gvi70000/STM32-DIY-Reflow-Soldering-Station/Core/Inc/gpio.h

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
/* Define to prevent recursive inclusion -------------------------------------*/
#ifndef __GPIO_H__
#define __GPIO_H__

#ifdef __cplusplus
extern "C" {
#endif

/* Includes ------------------------------------------------------------------*/
#include "main.h"

/* USER CODE BEGIN Private defines */
	extern volatile uint8_t BtnPressed;
	#define FAN_ON GPIOA->ODR |= GPIO_PIN_5;
	#define FAN_OFF GPIOA->ODR &= ~GPIO_PIN_5;
	#define HEAT_ON GPIOA->ODR |= GPIO_PIN_6;
	#define HEAT_OFF GPIOA->ODR &= ~GPIO_PIN_6;	
	#define BUZZ_ON GPIOA->ODR |= GPIO_PIN_7;
	#define BUZZ_OFF GPIOA->ODR &= ~GPIO_PIN_7;
	
/* USER CODE END Private defines */

void MX_GPIO_Init(void);

#ifdef __cplusplus
}
#endif
#endif /*__ GPIO_H__ */
