gvi70000/STM32-DIY-Reflow-Soldering-Station/Core/Src/adc.c

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
/* Includes ------------------------------------------------------------------*/
#include "adc.h"

/* USER CODE BEGIN 0 */
#include <math.h>
#include <stdio.h>
#define ONE					1.0f
#define TEMP_OFFSET	0.0f
#define K						273.15f //0°C in Kelvin
#define Beta				3950.0f //B-coefficient of the thermistor
#define ADC_RES			4096.0f //12 bit ADC value for 3.3V
#define T0					(K + 25.0f) //25°C in Kelvin
#define INV_T0			(ONE/T0) 
#define ADC_SIZE		64

//100k NTC measured resistance in Ohms @ 25C
const float R1[2] = {99000.0, 101000.0};
//10k resistor measured resistance in Ohms @ 25C
const float R2[2] = {10440, 10450.0};
//Calculated temperature
volatile float crtTemp, t1, t2;

uint16_t ntc1_Val[ADC_SIZE];
uint16_t ntc2_Val[ADC_SIZE];
/* USER CODE END 0 */

ADC_HandleTypeDef hadc1;
ADC_HandleTypeDef hadc2;
DMA_HandleTypeDef hdma_adc1;
DMA_HandleTypeDef hdma_adc2;

/* ADC1 init function */
void MX_ADC1_Init(void)
{

  ADC_MultiModeTypeDef multimode = {0};
  ADC_ChannelConfTypeDef sConfig = {0};

  /** Common config
  */
  hadc1.Instance = ADC1;
  hadc1.Init.ClockPrescaler = ADC_CLOCK_ASYNC_DIV1;
  hadc1.Init.Resolution = ADC_RESOLUTION_12B;
  hadc1.Init.ScanConvMode = ADC_SCAN_DISABLE;
  hadc1.Init.ContinuousConvMode = ENABLE;
  hadc1.Init.DiscontinuousConvMode = DISABLE;
  hadc1.Init.ExternalTrigConvEdge = ADC_EXTERNALTRIGCONVEDGE_NONE;
  hadc1.Init.ExternalTrigConv = ADC_SOFTWARE_START;
  hadc1.Init.DataAlign = ADC_DATAALIGN_RIGHT;
  hadc1.Init.NbrOfConversion = 1;
  hadc1.Init.DMAContinuousRequests = ENABLE;
  hadc1.Init.EOCSelection = ADC_EOC_SINGLE_CONV;
  hadc1.Init.LowPowerAutoWait = DISABLE;
  hadc1.Init.Overrun = ADC_OVR_DATA_OVERWRITTEN;
  if (HAL_ADC_Init(&hadc1) != HAL_OK)
  {
    Error_Handler();
  }

  /** Configure Regular Channel
  */
  sConfig.Channel = ADC_CHANNEL_4;
  sConfig.Rank = ADC_REGULAR_RANK_1;
  sConfig.SingleDiff = ADC_SINGLE_ENDED;
  sConfig.SamplingTime = ADC_SAMPLETIME_601CYCLES_5;
  sConfig.OffsetNumber = ADC_OFFSET_NONE;
  sConfig.Offset = 0;
  if (HAL_ADC_ConfigChannel(&hadc1, &sConfig) != HAL_OK)
  {
    Error_Handler();
  }
}
/* ADC2 init function */
void MX_ADC2_Init(void)
{

  ADC_ChannelConfTypeDef sConfig = {0};

  /** Common config
  */
  hadc2.Instance = ADC2;
  hadc2.Init.ClockPrescaler = ADC_CLOCK_ASYNC_DIV1;
  hadc2.Init.Resolution = ADC_RESOLUTION_12B;
  hadc2.Init.ScanConvMode = ADC_SCAN_DISABLE;
  hadc2.Init.ContinuousConvMode = ENABLE;
  hadc2.Init.DiscontinuousConvMode = DISABLE;
  hadc2.Init.ExternalTrigConvEdge = ADC_EXTERNALTRIGCONVEDGE_NONE;
  hadc2.Init.ExternalTrigConv = ADC_SOFTWARE_START;
  hadc2.Init.DataAlign = ADC_DATAALIGN_RIGHT;
  hadc2.Init.NbrOfConversion = 1;
  hadc2.Init.DMAContinuousRequests = ENABLE;
  hadc2.Init.EOCSelection = ADC_EOC_SINGLE_CONV;
  hadc2.Init.LowPowerAutoWait = DISABLE;
  hadc2.Init.Overrun = ADC_OVR_DATA_OVERWRITTEN;
  if (HAL_ADC_Init(&hadc2) != HAL_OK)
  {
    Error_Handler();
  }

  /** Configure Regular Channel
  */
  sConfig.Channel = ADC_CHANNEL_1;
  sConfig.Rank = ADC_REGULAR_RANK_1;
  sConfig.SingleDiff = ADC_SINGLE_ENDED;
  sConfig.SamplingTime = ADC_SAMPLETIME_601CYCLES_5;
  sConfig.OffsetNumber = ADC_OFFSET_NONE;
  sConfig.Offset = 0;
  if (HAL_ADC_ConfigChannel(&hadc2, &sConfig) != HAL_OK)
  {
    Error_Handler();
  }
}

static uint32_t HAL_RCC_ADC12_CLK_ENABLED=0;

void HAL_ADC_MspInit(ADC_HandleTypeDef* adcHandle)
{

  GPIO_InitTypeDef GPIO_InitStruct = {0};
  if(adcHandle->Instance==ADC1)
  {
    /* ADC1 clock enable */
    HAL_RCC_ADC12_CLK_ENABLED++;
    if(HAL_RCC_ADC12_CLK_ENABLED==1){
      __HAL_RCC_ADC12_CLK_ENABLE();
    }

    __HAL_RCC_GPIOA_CLK_ENABLE();
    /**ADC1 GPIO Configuration
    PA3     ------> ADC1_IN4
    */
    GPIO_InitStruct.Pin = NTC1_Pin;
    GPIO_InitStruct.Mode = GPIO_MODE_ANALOG;
    GPIO_InitStruct.Pull = GPIO_NOPULL;
    HAL_GPIO_Init(NTC1_GPIO_Port, &GPIO_InitStruct);

    /* ADC1 DMA Init */
    /* ADC1 Init */
    hdma_adc1.Instance = DMA1_Channel1;
    hdma_adc1.Init.Direction = DMA_PERIPH_TO_MEMORY;
    hdma_adc1.Init.PeriphInc = DMA_PINC_DISABLE;
    hdma_adc1.Init.MemInc = DMA_MINC_ENABLE;
    hdma_adc1.Init.PeriphDataAlignment = DMA_PDATAALIGN_HALFWORD;
    hdma_adc1.Init.MemDataAlignment = DMA_MDATAALIGN_HALFWORD;
    hdma_adc1.Init.Mode = DMA_CIRCULAR;
    hdma_adc1.Init.Priority = DMA_PRIORITY_LOW;
    if (HAL_DMA_Init(&hdma_adc1) != HAL_OK)
    {
      Error_Handler();
    }

    __HAL_LINKDMA(adcHandle,DMA_Handle,hdma_adc1);

  }
  else if(adcHandle->Instance==ADC2)
  {
    /* ADC2 clock enable */
    HAL_RCC_ADC12_CLK_ENABLED++;
    if(HAL_RCC_ADC12_CLK_ENABLED==1){
      __HAL_RCC_ADC12_CLK_ENABLE();
    }

    __HAL_RCC_GPIOA_CLK_ENABLE();
    /**ADC2 GPIO Configuration
    PA4     ------> ADC2_IN1
    */
    GPIO_InitStruct.Pin = NTC2_Pin;
    GPIO_InitStruct.Mode = GPIO_MODE_ANALOG;
    GPIO_InitStruct.Pull = GPIO_NOPULL;
    HAL_GPIO_Init(NTC2_GPIO_Port, &GPIO_InitStruct);

    /* ADC2 DMA Init */
    /* ADC2 Init */
    hdma_adc2.Instance = DMA2_Channel1;
    hdma_adc2.Init.Direction = DMA_PERIPH_TO_MEMORY;
    hdma_adc2.Init.PeriphInc = DMA_PINC_DISABLE;
    hdma_adc2.Init.MemInc = DMA_MINC_ENABLE;
    hdma_adc2.Init.PeriphDataAlignment = DMA_PDATAALIGN_HALFWORD;
    hdma_adc2.Init.MemDataAlignment = DMA_MDATAALIGN_HALFWORD;
    hdma_adc2.Init.Mode = DMA_CIRCULAR;
    hdma_adc2.Init.Priority = DMA_PRIORITY_LOW;
    if (HAL_DMA_Init(&hdma_adc2) != HAL_OK)
    {
      Error_Handler();
    }

    __HAL_LINKDMA(adcHandle,DMA_Handle,hdma_adc2);

  }
}

void HAL_ADC_MspDeInit(ADC_HandleTypeDef* adcHandle)
{

  if(adcHandle->Instance==ADC1)
  {
    /* Peripheral clock disable */
    HAL_RCC_ADC12_CLK_ENABLED--;
    if(HAL_RCC_ADC12_CLK_ENABLED==0){
      __HAL_RCC_ADC12_CLK_DISABLE();
    }

    /**ADC1 GPIO Configuration
    PA3     ------> ADC1_IN4
    */
    HAL_GPIO_DeInit(NTC1_GPIO_Port, NTC1_Pin);

    /* ADC1 DMA DeInit */
    HAL_DMA_DeInit(adcHandle->DMA_Handle);
  }
  else if(adcHandle->Instance==ADC2)
  {
    /* Peripheral clock disable */
    HAL_RCC_ADC12_CLK_ENABLED--;
    if(HAL_RCC_ADC12_CLK_ENABLED==0){
      __HAL_RCC_ADC12_CLK_DISABLE();
    }

    /**ADC2 GPIO Configuration
    PA4     ------> ADC2_IN1
    */
    HAL_GPIO_DeInit(NTC2_GPIO_Port, NTC2_Pin);

    /* ADC2 DMA DeInit */
    HAL_DMA_DeInit(adcHandle->DMA_Handle);
  }
}

/* USER CODE BEGIN 1 */
void startADC(){
	//Start ADC
	HAL_ADC_Start_DMA(&hadc1, (uint32_t*)ntc1_Val, ADC_SIZE);
	HAL_ADC_Start_DMA(&hadc2, (uint32_t*)ntc2_Val, ADC_SIZE);
}

void stopADC(){
	//Start ADC
	HAL_ADC_Stop(&hadc1);
	HAL_ADC_Stop(&hadc2);
}

static float calculateNTCTemperature(uint8_t idx, uint16_t* adcValues) {
  uint32_t sum = 0;
  for (uint8_t i = 0; i < ADC_SIZE; i++) {
    sum += adcValues[i];
  }
  float avgAdcValue = (float)sum / ADC_SIZE;
  float r_ntc = R2[idx] * (ADC_RES / avgAdcValue - 1.0);
  return (1.0 / (INV_T0 + 1.0 / Beta * log(r_ntc / R1[idx])) - K);
}

//Resistors as per link below, R1(Rntc) is the NTC and R2 is 100kOhm
//https://ohmslawcalculator.com/voltage-divider-calculator
void HAL_ADC_ConvCpltCallback(ADC_HandleTypeDef* hadc) {
  if (hadc->Instance == ADC1) {
    t1 = calculateNTCTemperature(0, ntc1_Val);
  }
  if (hadc->Instance == ADC2) {
    t2 = calculateNTCTemperature(1, ntc2_Val);
  }
	float medT = (t1 + t2) / 2.0;
	float medT2 = medT*medT;
  crtTemp = -0.0006*medT2 + 1.2193*medT +2.3892;
}
/* USER CODE END 1 */
