gvi70000/STM32-DIY-Reflow-Soldering-Station/ST7735/GFX_FUNCTIONS.c

#include <ST7735.h>
#include "stdint.h"
#include "stdlib.h"


extern uint8_t _width;       ///< Display width as modified by current rotation
extern uint8_t _height;      ///< Display height as modified by current rotation
extern uint8_t cursor_x;     ///< x location to start print()ing text
extern uint8_t cursor_y;     ///< y location to start print()ing text
extern uint8_t rotation;     ///< Display rotation (0 thru 3)
extern uint8_t _colstart;   ///< Some displays need this changed to offset
extern uint8_t _rowstart;       ///< Some displays need this changed to offset
extern uint8_t _xstart;
extern uint8_t _ystart;


void drawPixel(uint8_t x, uint8_t y, uint16_t color) {
	ST7735_DrawPixel(x, y, color);
}

void fillRect(uint8_t x, uint8_t y, uint8_t w, uint8_t h, uint16_t color) {
	ST7735_FillRectangle(x, y, w, h, color);
}


/***********************************************************************************************************/


#define _swap_int8_t(a, b)                                                    \
  {                                                                            \
    uint8_t t = a;                                                             \
    a = b;                                                                     \
    b = t;                                                                     \
  }

#define min(a, b) (((a) < (b)) ? (a) : (b))


void writePixel(uint8_t x, uint8_t y, uint16_t color) {
    drawPixel(x, y, color);
}

void writeLine(uint8_t x0, uint8_t y0, uint8_t x1, uint8_t y1, uint16_t color) {
    int8_t steep = abs(y1 - y0) > abs(x1 - x0);
    if (steep) {
        _swap_int8_t(x0, y0);
        _swap_int8_t(x1, y1);
    }

    if (x0 > x1) {
        _swap_int8_t(x0, x1);
        _swap_int8_t(y0, y1);
    }

    int8_t dx, dy;
    dx = x1 - x0;
    dy = abs(y1 - y0);

    int8_t err = dx / 2;
    int8_t ystep;

    if (y0 < y1) {
        ystep = 1;
    } else {
        ystep = -1;
    }

    for (; x0<=x1; x0++) {
        if (steep) {
            writePixel(y0, x0, color);
        } else {
            writePixel(x0, y0, color);
        }
        err -= dy;
        if (err < 0) {
            y0 += ystep;
            err += dx;
        }
    }
}

void  drawFastVLine(uint8_t x, uint8_t y, uint8_t h, uint16_t color) {
	writeLine(x, y, x, y + h - 1, color);
}
void  drawFastHLine(uint8_t x, uint8_t y, uint8_t w, uint16_t color) {
	writeLine(x, y, x + w - 1, y, color);
}

void drawLine(uint8_t x0, uint8_t y0, uint8_t x1, uint8_t y1, uint16_t color) {
    if(x0 == x1){
        if(y0 > y1) _swap_int8_t(y0, y1);
        drawFastVLine(x0, y0, y1 - y0 + 1, color);
    } else if(y0 == y1){
        if(x0 > x1) _swap_int8_t(x0, x1);
        drawFastHLine(x0, y0, x1 - x0 + 1, color);
    } else {
        writeLine(x0, y0, x1, y1, color);
    }
}

void drawCircle(uint8_t x0, uint8_t y0, uint8_t r, uint16_t color) {
    uint8_t f = 1 - r;
    uint8_t ddF_x = 1;
    uint8_t ddF_y = -2 * r;
    uint8_t x = 0;
    uint8_t y = r;

    writePixel(x0  , y0+r, color);
    writePixel(x0  , y0-r, color);
    writePixel(x0+r, y0  , color);
    writePixel(x0-r, y0  , color);

    while (x<y) {
        if (f >= 0) {
            y--;
            ddF_y += 2;
            f += ddF_y;
        }
        x++;
        ddF_x += 2;
        f += ddF_x;

        writePixel(x0 + x, y0 + y, color);
        writePixel(x0 - x, y0 + y, color);
        writePixel(x0 + x, y0 - y, color);
        writePixel(x0 - x, y0 - y, color);
        writePixel(x0 + y, y0 + x, color);
        writePixel(x0 - y, y0 + x, color);
        writePixel(x0 + y, y0 - x, color);
        writePixel(x0 - y, y0 - x, color);
    }
}

void drawCircleHelper(uint8_t x0, uint8_t y0, uint8_t r, uint8_t cornername, uint16_t color) {
    uint8_t f     = 1 - r;
    uint8_t ddF_x = 1;
    uint8_t ddF_y = -2 * r;
    uint8_t x     = 0;
    uint8_t y     = r;

    while (x<y) {
        if (f >= 0) {
            y--;
            ddF_y += 2;
            f     += ddF_y;
        }
        x++;
        ddF_x += 2;
        f     += ddF_x;
        if (cornername & 0x4) {
            writePixel(x0 + x, y0 + y, color);
            writePixel(x0 + y, y0 + x, color);
        }
        if (cornername & 0x2) {
            writePixel(x0 + x, y0 - y, color);
            writePixel(x0 + y, y0 - x, color);
        }
        if (cornername & 0x8) {
            writePixel(x0 - y, y0 + x, color);
            writePixel(x0 - x, y0 + y, color);
        }
        if (cornername & 0x1) {
            writePixel(x0 - y, y0 - x, color);
            writePixel(x0 - x, y0 - y, color);
        }
    }
}

void fillCircleHelper(uint8_t x0, uint8_t y0, uint8_t r, uint8_t corners, uint8_t delta, uint16_t color) {

    uint8_t f     = 1 - r;
    uint8_t ddF_x = 1;
    uint8_t ddF_y = -2 * r;
    uint8_t x     = 0;
    uint8_t y     = r;
    uint8_t px    = x;
    uint8_t py    = y;

    delta++; // Avoid some +1's in the loop

    while(x < y) {
        if (f >= 0) {
            y--;
            ddF_y += 2;
            f     += ddF_y;
        }
        x++;
        ddF_x += 2;
        f     += ddF_x;
        // These checks avoid double-drawing certain lines, important
        // for the SSD1306 library which has an INVERT drawing mode.
        if(x < (y + 1)) {
            if(corners & 1) drawFastVLine(x0+x, y0-y, 2*y+delta, color);
            if(corners & 2) drawFastVLine(x0-x, y0-y, 2*y+delta, color);
        }
        if(y != py) {
            if(corners & 1) drawFastVLine(x0+py, y0-px, 2*px+delta, color);
            if(corners & 2) drawFastVLine(x0-py, y0-px, 2*px+delta, color);
            py = y;
        }
        px = x;
    }
}

void fillCircle(uint8_t x0, uint8_t y0, uint8_t r, uint16_t color) {
    drawFastVLine(x0, y0-r, 2*r+1, color);
    fillCircleHelper(x0, y0, r, 3, 0, color);
}



void drawRect(uint8_t x, uint8_t y, uint8_t w, uint8_t h, uint16_t color) {
    drawFastHLine(x, y, w, color);
    drawFastHLine(x, y+h-1, w, color);
    drawFastVLine(x, y, h, color);
    drawFastVLine(x+w-1, y, h, color);
}

void drawRoundRect(uint8_t x, uint8_t y, uint8_t w, uint8_t h, uint8_t r, uint16_t color) {
    uint8_t max_radius = ((w < h) ? w : h) / 2; // 1/2 minor axis
    if(r > max_radius) r = max_radius;
    // smarter version
    drawFastHLine(x+r  , y    , w-2*r, color); // Top
    drawFastHLine(x+r  , y+h-1, w-2*r, color); // Bottom
    drawFastVLine(x    , y+r  , h-2*r, color); // Left
    drawFastVLine(x+w-1, y+r  , h-2*r, color); // Right
    // draw four corners
    drawCircleHelper(x+r    , y+r    , r, 1, color);
    drawCircleHelper(x+w-r-1, y+r    , r, 2, color);
    drawCircleHelper(x+w-r-1, y+h-r-1, r, 4, color);
    drawCircleHelper(x+r    , y+h-r-1, r, 8, color);
}


void fillRoundRect(uint8_t x, uint8_t y, uint8_t w, uint8_t h, uint8_t r, uint16_t color) {
    uint8_t max_radius = ((w < h) ? w : h) / 2; // 1/2 minor axis
    if(r > max_radius) r = max_radius;
    // smarter version
    fillRect(x+r, y, w-2*r, h, color);
    // draw four corners
    fillCircleHelper(x+w-r-1, y+r, r, 1, h-2*r-1, color);
    fillCircleHelper(x+r    , y+r, r, 2, h-2*r-1, color);
}


void drawTriangle(uint8_t x0, uint8_t y0, uint8_t x1, uint8_t y1, uint8_t x2, uint8_t y2, uint16_t color) {
    drawLine(x0, y0, x1, y1, color);
    drawLine(x1, y1, x2, y2, color);
    drawLine(x2, y2, x0, y0, color);
}


void fillTriangle(uint8_t x0, uint8_t y0, uint8_t x1, uint8_t y1, uint8_t x2, uint8_t y2, uint16_t color) {

    int16_t a, b, y, last;

    // Sort coordinates by Y order (y2 >= y1 >= y0)
    if (y0 > y1) {
        _swap_int8_t(y0, y1); _swap_int8_t(x0, x1);
    }
    if (y1 > y2) {
        _swap_int8_t(y2, y1); _swap_int8_t(x2, x1);
    }
    if (y0 > y1) {
        _swap_int8_t(y0, y1); _swap_int8_t(x0, x1);
    }

    if(y0 == y2) { // Handle awkward all-on-same-line case as its own thing
        a = b = x0;
        if(x1 < a)      a = x1;
        else if(x1 > b) b = x1;
        if(x2 < a)      a = x2;
        else if(x2 > b) b = x2;
        drawFastHLine(a, y0, b-a+1, color);
        return;
    }

    int16_t
    dx01 = x1 - x0,
    dy01 = y1 - y0,
    dx02 = x2 - x0,
    dy02 = y2 - y0,
    dx12 = x2 - x1,
    dy12 = y2 - y1;
    int32_t
    sa   = 0,
    sb   = 0;

    // For upper part of triangle, find scanline crossings for segments
    // 0-1 and 0-2.  If y1=y2 (flat-bottomed triangle), the scanline y1
    // is included here (and second loop will be skipped, avoiding a /0
    // error there), otherwise scanline y1 is skipped here and handled
    // in the second loop...which also avoids a /0 error here if y0=y1
    // (flat-topped triangle).
    if(y1 == y2) last = y1;   // Include y1 scanline
    else         last = y1-1; // Skip it

    for(y=y0; y<=last; y++) {
        a   = x0 + sa / dy01;
        b   = x0 + sb / dy02;
        sa += dx01;
        sb += dx02;
        /* longhand:
        a = x0 + (x1 - x0) * (y - y0) / (y1 - y0);
        b = x0 + (x2 - x0) * (y - y0) / (y2 - y0);
        */
        if(a > b) _swap_int8_t(a,b);
        drawFastHLine(a, y, b-a+1, color);
    }

    // For lower part of triangle, find scanline crossings for segments
    // 0-2 and 1-2.  This loop is skipped if y1=y2.
    sa = (int32_t)dx12 * (y - y1);
    sb = (int32_t)dx02 * (y - y0);
    for(; y<=y2; y++) {
        a   = x1 + sa / dy12;
        b   = x0 + sb / dy02;
        sa += dx12;
        sb += dx02;
        /* longhand:
        a = x1 + (x2 - x1) * (y - y1) / (y2 - y1);
        b = x0 + (x2 - x0) * (y - y0) / (y2 - y0);
        */
        if(a > b) _swap_int8_t(a,b);
        drawFastHLine(a, y, b-a+1, color);
    }
}

void fillScreen(uint16_t color) {
    fillRect(0, 0, _width, _height, color);
}

void drawButton(uint8_t x, uint8_t y, uint8_t w, uint8_t h, uint16_t borderColor, uint16_t fillColor, uint16_t txtColor, const char* txt){
	drawRoundRect(x, y, w, h, 4, borderColor);
	fillRoundRect(x+1, y+1, w-2, h-2, 3, fillColor);
	ST7735_WriteString(x+7, y+6, txt, Font_7x10, txtColor, fillColor);
}
