gvi70000/STM32-DIY-Reflow-Soldering-Station/ST7735/ST7735.h

#ifndef __ST7735_H__
#define __ST7735_H__

#include "fonts.h"
#include "stm32f3xx_hal.h"
#include <stdbool.h>


extern SPI_HandleTypeDef hspi2;
#define ST7735_USE_DMA
#define ST7735_SPI_PORT hspi2

/****** TFT DEFINES ******/
//#define ST7735_IS_160X80 1
//#define ST7735_IS_128X128 1
#define ST7735_IS_160X128	1
#define ST7735_WIDTH			128
#define ST7735_HEIGHT			160

#define DELAY 0x80

#define ST7735_MADCTL_MY	0x80
#define ST7735_MADCTL_MX	0x40
#define ST7735_MADCTL_MV	0x20
#define ST7735_MADCTL_ML	0x10
#define ST7735_MADCTL_RGB	0x00
#define ST7735_MADCTL_BGR	0x08
#define ST7735_MADCTL_MH  0x04

#define ST7735_NOP				0x00
#define ST7735_SWRESET		0x01
#define ST7735_RDDID			0x04
#define ST7735_RDDST			0x09

#define ST7735_SLPIN			0x10
#define ST7735_SLPOUT			0x11
#define ST7735_PTLON			0x12
#define ST7735_NORON			0x13

#define ST7735_INVOFF			0x20
#define ST7735_INVON			0x21
#define ST7735_DISPOFF		0x28
#define ST7735_DISPON			0x29
#define ST7735_CASET			0x2A
#define ST7735_RASET			0x2B
#define ST7735_RAMWR			0x2C
#define ST7735_RAMRD			0x2E

#define ST7735_PTLAR			0x30
#define ST7735_COLMOD			0x3A
#define ST7735_MADCTL			0x36

#define ST7735_FRMCTR1		0xB1
#define ST7735_FRMCTR2		0xB2
#define ST7735_FRMCTR3		0xB3
#define ST7735_INVCTR			0xB4
#define ST7735_DISSET5		0xB6

#define ST7735_PWCTR1			0xC0
#define ST7735_PWCTR2			0xC1
#define ST7735_PWCTR3			0xC2
#define ST7735_PWCTR4			0xC3
#define ST7735_PWCTR5			0xC4
#define ST7735_VMCTR1			0xC5

#define ST7735_RDID1			0xDA
#define ST7735_RDID2			0xDB
#define ST7735_RDID3			0xDC
#define ST7735_RDID4			0xDD

#define ST7735_PWCTR6			0xFC

#define ST7735_GMCTRP1		0xE0
#define ST7735_GMCTRN1		0xE1

// Color definitions
#define BLACK       			0x0000
#define BLUE        			0x001F
#define RED         			0xF800
#define GREEN       			0x07E0
#define CYAN        			0x07FF
#define MAGENTA     			0xF81F
#define YELLOW      			0xFFE0
#define ORANGE 						0xFD20
#define PEACH 						0xFF7B
#define WHITE       			0xFFFF

#define CMD_SIZE  				1
#define COLOR_SIZE  			2
#define COORD_SIZE  			4

#define INT_TO_BYTES(value, data) \
	do { \
		data[0] = (value >> 8) & 0xFF; \
		data[1] = value & 0xFF; \
	} while (0)
		
#define color565(r, g, b) (((r & 0xF8) << 8) | ((g & 0xFC) << 3) | ((b & 0xF8) >> 3))
#define _swap_int8_t(a, b) \
  { \
    uint8_t t = a; \
    a = b; \
    b = t; \
  }

#define min(a, b) (((a) < (b)) ? (a) : (b))
	
#define ST7735_Unselect	GPIOA->ODR |= LCD_CS_Pin;
#define ST7735_Select		GPIOA->ODR &= ~LCD_CS_Pin;

#define LCD_RST_ON GPIOA->ODR |= GPIO_PIN_8;
#define LCD_RST_OFF GPIOA->ODR &= ~GPIO_PIN_8;

#define LCD_CMD_ON GPIOB->ODR |= GPIO_PIN_12;
#define LCD_CMD_OFF GPIOB->ODR &= ~GPIO_PIN_12;

// call before initializing any SPI devices

void ST7735_Init(uint8_t rotation);
void ST7735_SetRotation(uint8_t m);
void ST7735_DrawPixel(uint8_t x, uint8_t y, uint16_t color);
void ST7735_WriteString(uint8_t x, uint8_t y, const char* str, FontDef font, uint16_t color, uint16_t bgcolor);
void ST7735_FillRectangle(uint8_t x, uint8_t y, uint8_t w, uint8_t h, uint16_t color);
void ST7735_FillScreen(uint16_t color);
void ST7735_InvertColors(bool invert);
void fillScreen(uint16_t color);
void drawLine(uint8_t x0, uint8_t y0, uint8_t x1, uint8_t y1, uint16_t color);

void  drawFastVLine(uint8_t x, uint8_t y, uint8_t h, uint16_t color);
void  drawFastHLine(uint8_t x, uint8_t y, uint8_t w, uint16_t color);
void drawRect(uint8_t x, uint8_t y, uint8_t w, uint8_t h, uint16_t color);
void drawButton(uint8_t x, uint8_t y, uint8_t w, uint8_t h, uint16_t fillColor, uint16_t txtColor, const char* txt);
#endif // __ST7735_H__
